BoujeeEnjinia1701/cellcheck/cad/drawings/CCK-DWG-001.pdf

CONCEPT, NOT FOR FABRICATION | CellCheck · github.com/BoujeeEnjinia1701/cellcheck

FRONT VIEW
Scale 1:5; looking at the front (along +Y)

TOP VIEW
Scale 1:5; looking down (along -Z)

RIGHT VIEW
Scale 1:5; looking at the right side (along -X)

460

300 85

ISOMETRIC VIEW
Not to scale; the cells sit under the perforated guard; seen from the front right and above, about 30 deg elevation

KEY DIMENSIONS AND INTERFACES (MM)
Unit envelope 460 x 300 x 85 on six 8 mm rubber feet
Tray 1.5 steel, liner 3; plate 1.5 Al on six 12 mm standoffs
8 channels at 40 pitch, channel 1 at x -170; cells along Y Holders take 18650 and 21700 (to 70 long, 21 dia), four-wire Guard 320 x 100 x 48.5; two M4 thumb screws
Heatsink 320 x 36 x 50: 40 fins at 8 pitch
2 fans 60 mm, finger guards, on a folded shroud on the spine ends Fan intake slots 56 x 22 in tray back wall
16 wire slots in the plate, silicone sealed
12 V DC inlet only, 6.3 A fuse; 3 A fuse per cell
Watchdog and 2.5 V comparator board (item 18) Rest rack (48 cells) and adapter stand beside the tray Mass about 4.94 kg without adapter (CCK-CAL-001) PRELIMINARY, NOT FOR FABRICATION
REV | DESCRIPTION | DATE | BY
P1 | Preliminary GA (CCK-CAL-001, CCK-DDR-001) | 2026-09-25 | AC
P2 | Constructable design: feet, standoffs, fixings (CCK-DDR-003) | 2026-10-01 | AC
P3 | Fan finger guards, silicone-sealed wire slots (CCK-DEC-001) | 2026-10-02 | AC
CELLCHECK | github.com/BoujeeEnjinia1701/cellcheck

## General arrangement, eight-channel grader

DRAWING NO.
CCK-DWG-001

REV
P3

SHEET
1 of 1

SIZE

## ANSI B

SCALE
1:5

UNITS
mm
PROJECTION | DATE
2026-10-02

DRAWN
Amish Chadha

MATERIAL / NOTES
Tray 1.5 mm steel; plate 1.5 mm Al; heatsink Al; guard 0.8 mm perforated steel. See bom/bom.csv
Licensed CERN-OHL-S-2.0 · Design Molecule Lab · designmolecule.com | Generated from cad/src; do not edit by hand
