BoujeeEnjinia1701/cellcheck/cad/drawings/CCK-DWG-101.pdf

### BUILD PLAN SKETCH, PLAN NOT YET BUILT CellCheck · github.com/BoujeeEnjinia1701/cellcheck

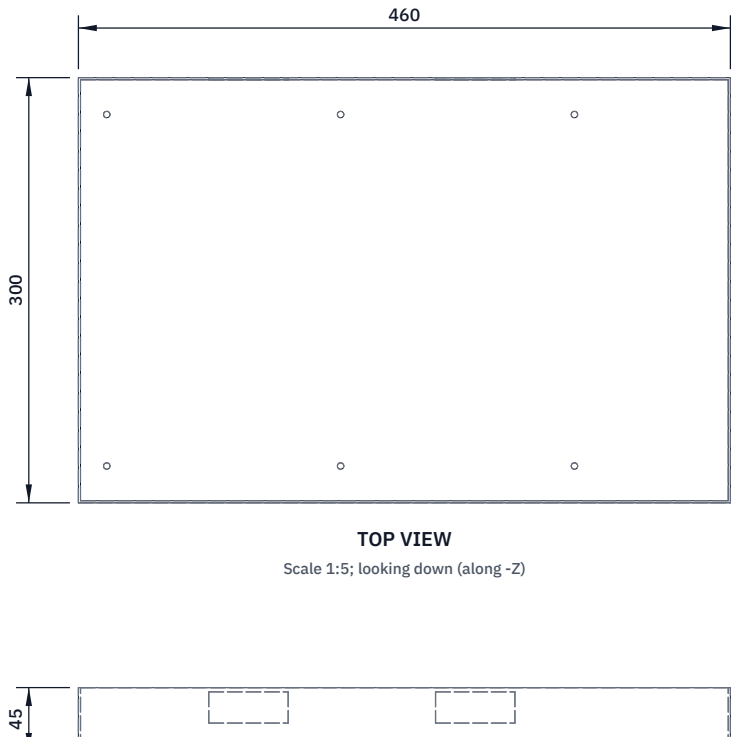
[picture p40: figure]
TOP VIEW; Scale 1:5; looking down (along -Z)

FRONT VIEW
Scale 1:5; looking at the front (along +Y)

RIGHT VIEW
Scale 1:5; looking at the right side (along -X)

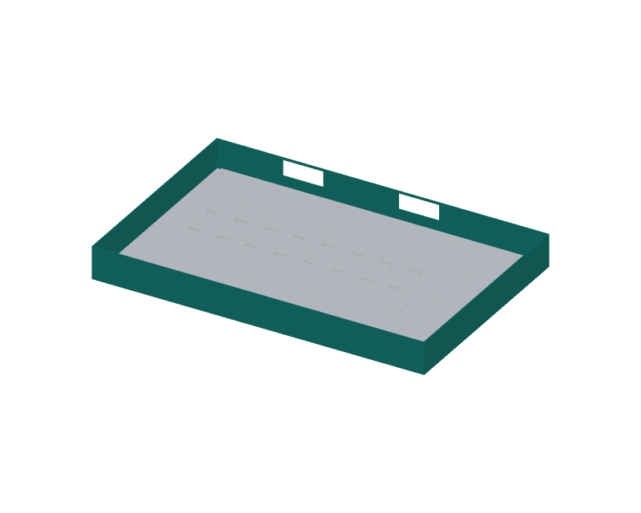
[picture p41: figure]

WHERE IT GOES
This part in colour, its neighbours in grey

HOW TO MAKE IT AND HOW IT FITS
Buy a plain steel tray about 460 x 300 x 45 mm, 1.5 mm wall, with a flat floor at least 457 x 297 mm inside. No plastic coating.
Two fan intake slots in the back wall, 56 wide x 22 tall, from 20 to 42 mm up from the floor, centred 110 mm left and 50 mm right of the centre. Drill 6 mm in each corner, cut between with a hacksaw or nibbler, file. Six 4.5 mm holes in the floor for the foot studs, 124 mm each side of
the centre line front to back, at 210 mm left, 45 mm left and
120 mm right of centre. Measure from the centre lines you scribe. Deburr every cut edge inside and out; touch up bare steel with paint. Fit: a rubber foot under each hole; its stud goes up into a standoff. Check: the six holes match the base plate's corner holes when the plate is laid on top, centred, before the liner goes in.
REV | DESCRIPTION | DATE | BY
P1 | Making sketch for the prototype build plan | 2026-10-02 | AC
CELLCHECK | github.com/BoujeeEnjinia1701/cellcheck

## CellCheck steel tray (bought, cut and drilled): making sketch

DRAWING NO.
CCK-DWG-101

REV
P1

SHEET
1 of 1

SIZE

## ANSI B

SCALE
1:5

UNITS
mm
PROJECTION | DATE
2026-10-02

DRAWN
Amish Chadha

MATERIAL / NOTES
Bought steel tray 460 x 300 x 45 mm, 1.5 mm wall
Licensed CERN-OHL-S-2.0 · Design Molecule Lab · designmolecule.com | Generated from cad/src; do not edit by hand
