BoujeeEnjinia1701/cellcheck/cad/drawings/CCK-DWG-102.pdf

### BUILD PLAN SKETCH, PLAN NOT YET BUILT CellCheck · github.com/BoujeeEnjinia1701/cellcheck

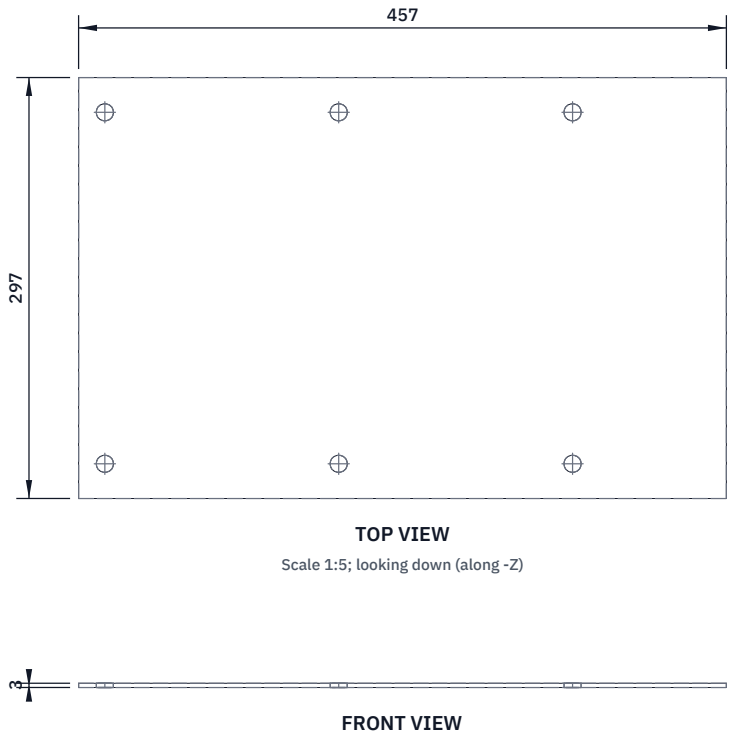
[picture p42: figure]
FRONT VIEW; TOP VIEW; Scale 1:5; looking down (along -Z)

Scale 1:5; looking at the front (along +Y)

RIGHT VIEW
Scale 1:5; looking at the right side (along -X)

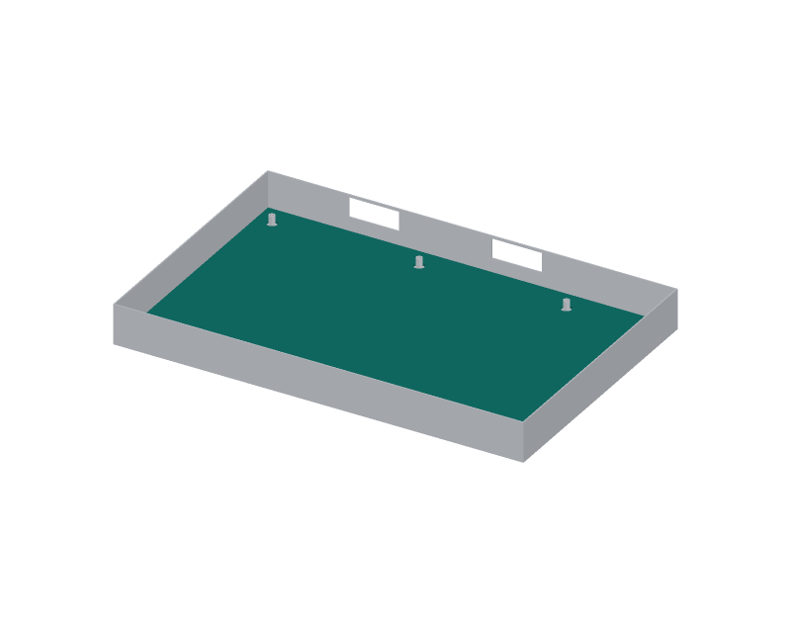
[picture p43: figure]

WHERE IT GOES
This part in colour, its neighbours in grey

HOW TO MAKE IT AND HOW IT FITS
Cut 457 x 297 mm from 3 mm ceramic fibre sheet with a sharp knife and a steel rule; trim so it lies flat on the tray floor.
Six 12 mm holes at the standoff positions (the same places as the tray's stud holes): 124 mm each side front to back, at 210 left,
45 left and 120 right of centre. Cut with a 12 mm hole punch or knife. Wear a dust mask (FFP2 or N95), gloves and long sleeves; cut outdoors or with dust extraction; wet-wipe the bench afterwards.
Fit: lies loose on the floor round the standoffs, 2 mm clear of each. Check: no tears; the floor is covered except at the six holes.
REV | DESCRIPTION | DATE | BY
P1 | Making sketch for the prototype build plan | 2026-10-02 | AC
CELLCHECK | github.com/BoujeeEnjinia1701/cellcheck

## CellCheck ceramic fibre liner: making sketch

DRAWING NO.
CCK-DWG-102

REV
P1

SHEET
1 of 1

SIZE

## ANSI B

SCALE
1:5

UNITS
mm
PROJECTION | DATE
2026-10-02

DRAWN
Amish Chadha

MATERIAL / NOTES
Ceramic fibre sheet 3 mm
Licensed CERN-OHL-S-2.0 · Design Molecule Lab · designmolecule.com | Generated from cad/src; do not edit by hand
