BoujeeEnjinia1701/cellcheck/cad/drawings/CCK-DWG-103.pdf

### BUILD PLAN SKETCH, PLAN NOT YET BUILT CellCheck · github.com/BoujeeEnjinia1701/cellcheck

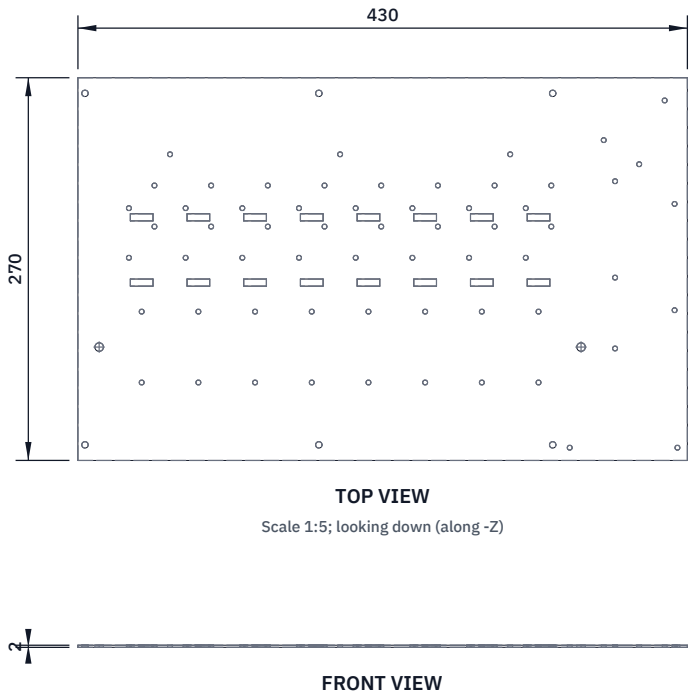
[picture p44: figure]
FRONT VIEW; TOP VIEW; Scale 1:5; looking down (along -Z)

Scale 1:5; looking at the front (along +Y)

RIGHT VIEW
Scale 1:5; looking at the right side (along -X)

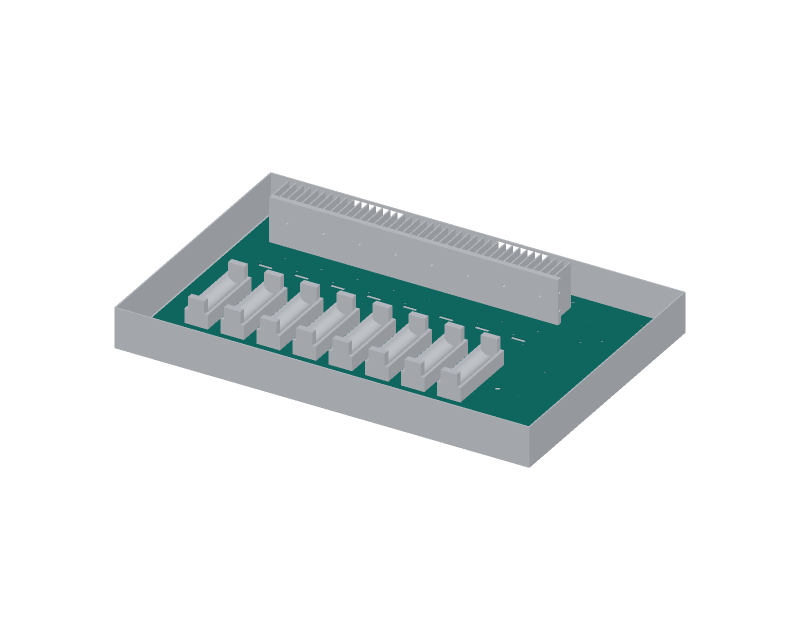
[picture p45: figure]

WHERE IT GOES
This part in colour, its neighbours in grey

HOW TO MAKE IT AND HOW IT FITS
Blank 430 x 270 mm, 1.5 mm aluminium; round the corners to 3 mm. Measure every hole from the left edge and the front edge; the
hole layout picture in the build plan gives every position.
Six 4.5 mm holes for the standoffs, 11 mm from the front and back. Per channel (eight channels, 40 mm apart, first at 45 mm from the left): two 3.4 mm holder screw holes; a 16 x 5 mm wire slot behind the holder and another between the charger and the channel board;
four 3.4 mm holes for the board standoffs.
Two 6 mm holes for the guard rivet nuts; set M4 rivet nuts in them. Three 3.4 mm heatsink screw holes; 3.4 mm holes for the right-hand bay. Slots: drill 5 mm at each end, cut between, file; fit edge grommet strip. After wiring, each slot is filled with silicone round the leads.
Check: lay the holders and heatsink on it and look through each hole.
REV | DESCRIPTION | DATE | BY
P1 | Making sketch for the prototype build plan | 2026-10-02 | AC
CELLCHECK | github.com/BoujeeEnjinia1701/cellcheck

## CellCheck base plate: making sketch

DRAWING NO.
CCK-DWG-103

REV
P1

SHEET
1 of 1

SIZE

## ANSI B

SCALE
1:5

UNITS
mm
PROJECTION | DATE
2026-10-02

DRAWN
Amish Chadha

MATERIAL / NOTES
Aluminium sheet 1.5 mm, 5052 or 6061 class
Licensed CERN-OHL-S-2.0 · Design Molecule Lab · designmolecule.com | Generated from cad/src; do not edit by hand
