BoujeeEnjinia1701/cellcheck/cad/drawings/CCK-DWG-104.pdf

### BUILD PLAN SKETCH, PLAN NOT YET BUILT CellCheck · github.com/BoujeeEnjinia1701/cellcheck

FRONT VIEW
Scale 1:2; looking at the front (along +Y)

TOP VIEW
Scale 1:2; looking down (along -Z)

RIGHT VIEW
Scale 1:2; looking at the right side (along -X)

320

36 50

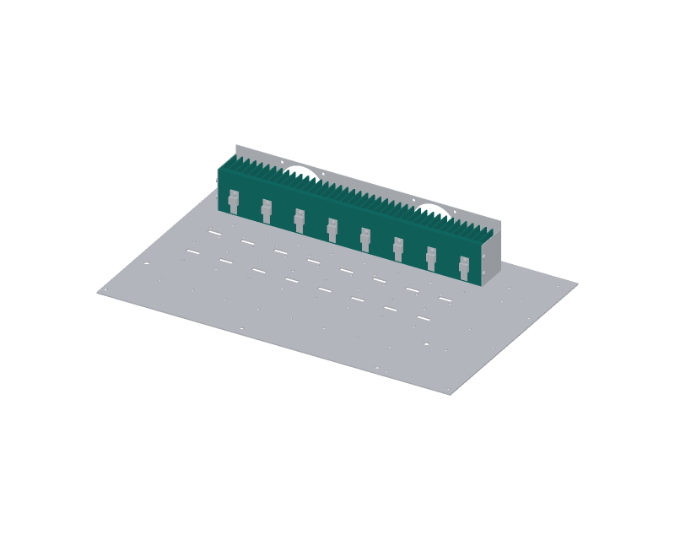
[picture p46: figure]

WHERE IT GOES
This part in colour, its neighbours in grey

HOW TO MAKE IT AND HOW IT FITS
Bought: a 6 mm spine 320 x 50 mm with 40 fins 30 mm deep at 8 mm pitch. MOSFET holes: eight M3 tapped holes through the spine (drill 2.5),
26.5 mm up from the bottom edge, 20 mm from the left end and then
every 40 mm, each midway between two fins. Deburr the front face flat. Plate screws: three M3 tapped holes 10 mm deep in the bottom edge, centred in the spine's 6 mm thickness, 40, 160 and 280 mm from the left end. Shroud screws: two M3 tapped holes 8 mm deep in each end of the spine, centred in its thickness, 15 and 35 mm up from the bottom edge.
Use cutting fluid; back the tap out often; the walls are thin.
Fit: stands on the plate, fins to the back; MOSFETs on the smooth face. Check: an M3 screw runs freely into every hole.
REV | DESCRIPTION | DATE | BY
P1 | Making sketch for the prototype build plan | 2026-10-02 | AC
CELLCHECK | github.com/BoujeeEnjinia1701/cellcheck

## CellCheck heatsink (bought, drilled and tapped): making sketch

DRAWING NO.
CCK-DWG-104

REV
P1

SHEET
1 of 1

SIZE

## ANSI B

SCALE
1:2

UNITS
mm
PROJECTION | DATE
2026-10-02

DRAWN
Amish Chadha

MATERIAL / NOTES
Aluminium finned heatsink 320 x 36 x 50 mm
Licensed CERN-OHL-S-2.0 · Design Molecule Lab · designmolecule.com | Generated from cad/src; do not edit by hand
