BoujeeEnjinia1701/cellcheck/cad/drawings/CCK-DWG-105.pdf

### BUILD PLAN SKETCH, PLAN NOT YET BUILT CellCheck · github.com/BoujeeEnjinia1701/cellcheck

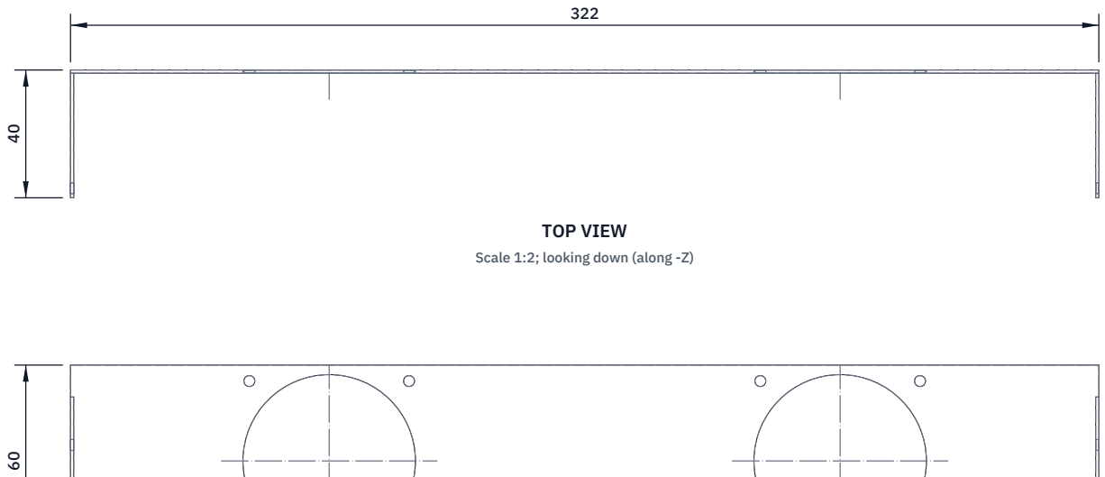
[picture p47: figure]
TOP VIEW; Scale 1:2; looking down (along -Z)
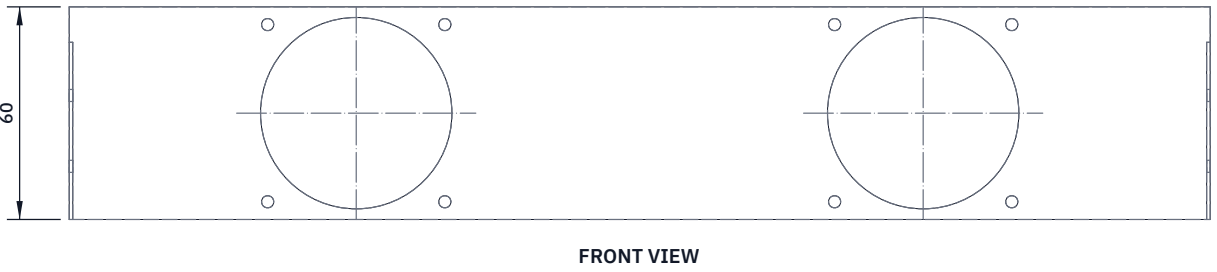
[picture p48: figure]
FRONT VIEW

Scale 1:2; looking at the front (along +Y)

RIGHT VIEW
Scale 1:2; looking at the right side (along -X)

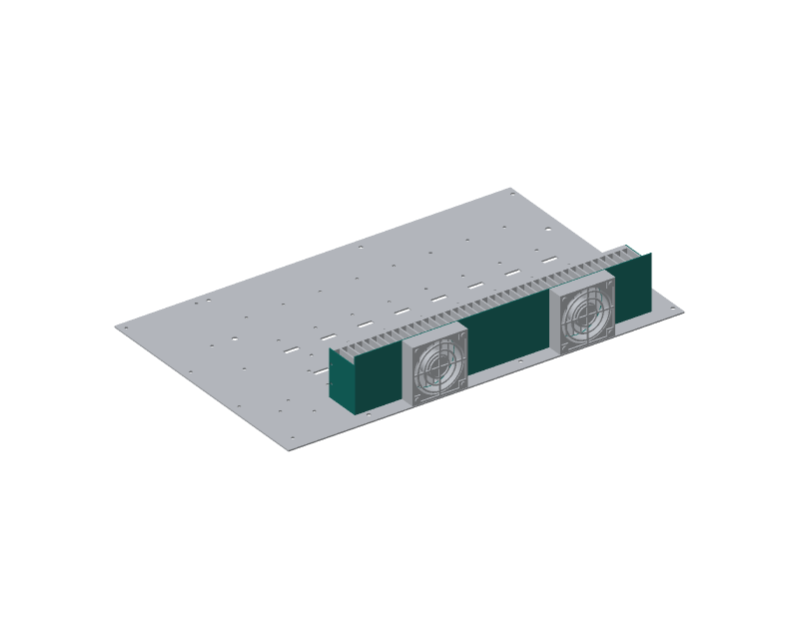
[picture p49: figure]

WHERE IT GOES
This part in colour, its neighbours in grey

HOW TO MAKE IT AND HOW IT FITS
One blank 322 x 60 mm back with a 39 x 50 mm flange on each end. Two 54 mm fan holes, centred 30 mm up, 81 mm and 241 mm from the left end of the back; cut with a hole saw or step drill.
Fan screw holes 3.4 mm on a 50 mm square round each fan hole. Fold each end flange 90 degrees forward, square to the back.
Two 3.4 mm holes in each flange, 3 mm from the free end (in line with the spine), 15 and 35 mm up from the bottom edge.
Fit the fans to the back first, screws from the inside; each fan gets a 60 mm finger guard on its outer face (four small screws). Fit: the flanges lie on the spine ends; the back stands 3 mm behind the fins; the bottom edge rests on the plate.
Check: the flange holes line up with the tapped holes in the spine.
REV | DESCRIPTION | DATE | BY
P1 | Making sketch for the prototype build plan | 2026-10-02 | AC
CELLCHECK | github.com/BoujeeEnjinia1701/cellcheck

## CellCheck fan shroud: making sketch

DRAWING NO.
CCK-DWG-105

REV
P1

SHEET
1 of 1

SIZE

## ANSI B

SCALE
1:2

UNITS
mm
PROJECTION | DATE
2026-10-02

DRAWN
Amish Chadha

MATERIAL / NOTES
Aluminium sheet 1 mm
Licensed CERN-OHL-S-2.0 · Design Molecule Lab · designmolecule.com | Generated from cad/src; do not edit by hand
