BoujeeEnjinia1701/cellcheck/cad/drawings/CCK-DWG-106.pdf

### BUILD PLAN SKETCH, PLAN NOT YET BUILT CellCheck · github.com/BoujeeEnjinia1701/cellcheck

FRONT VIEW
Scale 1:1; looking at the front (along +Y)

TOP VIEW
Scale 1:1; looking down (along -Z)

RIGHT VIEW
Scale 1:1; looking at the right side (along -X)

88

25 62

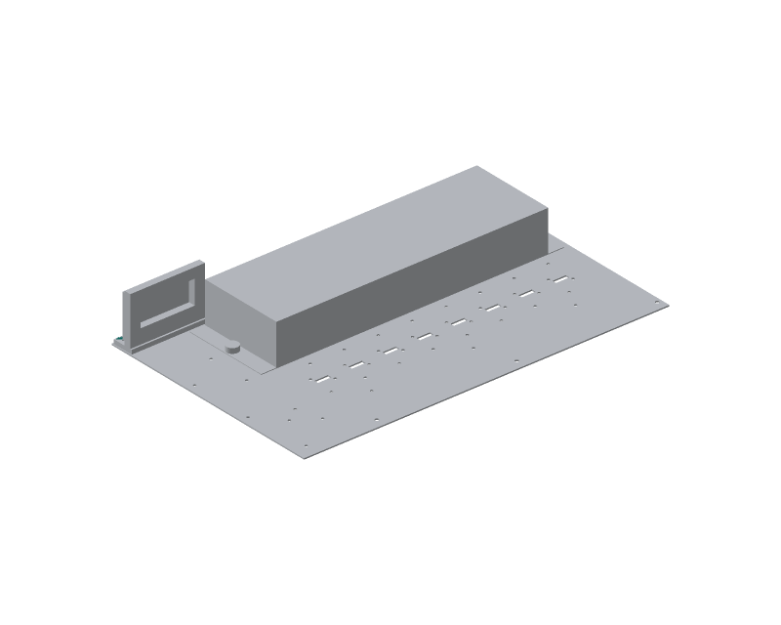
[picture p50: figure]

WHERE IT GOES
This part in colour, its neighbours in grey

HOW TO MAKE IT AND HOW IT FITS
Print: a foot 88 x 25 x 5 mm and an upright 88 x 8 x 62 mm,
15 mm back from the foot's front edge, printed lying on its back. Window 64 x 28 mm in the upright, 22 mm up, for the display's pins. Two 3 mm pilot holes in the foot, 6 mm in from each end and 7 mm from the front, for M3 screws from under the plate.
Three 7 mm holes in the foot's front strip, 25 mm apart, for the panel-mount push buttons, held by their nuts.
Fit: the display module screws to the upright's front face with its four corner holes (M2.5 or M3 self-tappers).
Check: the 86 x 50 mm display board sits flat on the upright.
REV | DESCRIPTION | DATE | BY
P1 | Making sketch for the prototype build plan | 2026-10-02 | AC
CELLCHECK | github.com/BoujeeEnjinia1701/cellcheck

## CellCheck display stand: making sketch

DRAWING NO.
CCK-DWG-106

REV
P1

SHEET
1 of 1

SIZE

## ANSI B

SCALE
1:1

UNITS
mm
PROJECTION | DATE
2026-10-02

DRAWN
Amish Chadha

MATERIAL / NOTES
PETG, 3D printed, 40 % infill
Licensed CERN-OHL-S-2.0 · Design Molecule Lab · designmolecule.com | Generated from cad/src; do not edit by hand
