BoujeeEnjinia1701/cellcheck/cad/drawings/CCK-DWG-107.pdf

### BUILD PLAN SKETCH, PLAN NOT YET BUILT CellCheck · github.com/BoujeeEnjinia1701/cellcheck

FRONT VIEW
Scale 1:1; looking at the front (along +Y)

TOP VIEW
Scale 1:1; looking down (along -Z)

RIGHT VIEW
Scale 1:1; looking at the right side (along -X)

55

40 28

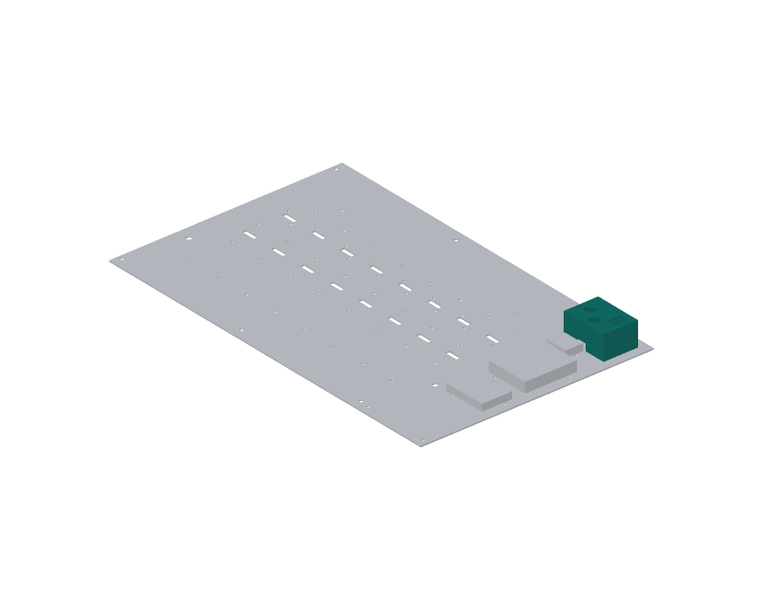
[picture p51: figure]

WHERE IT GOES
This part in colour, its neighbours in grey

HOW TO MAKE IT AND HOW IT FITS
Print an open-bottomed box 55 x 40 x 28 mm, 2 mm walls, top up. Top face: DC jack hole 11.2 mm; fuse holder hole 12 mm;
rocker switch cut-out 12 x 16 mm (check each against its datasheet). Wire exit notch 20 x 8 mm at the bottom of the front wall.
Two screw bosses inside, 6 mm in from opposite corners, 3 mm pilot holes for M3 screws from under the plate.
Fit: jack, fuse holder and switch go in from the top, nuts inside.
The adapter lead comes over the tray's right rim into the jack. Check: each part snaps or screws in square; nothing rocks.
REV | DESCRIPTION | DATE | BY
P1 | Making sketch for the prototype build plan | 2026-10-02 | AC
CELLCHECK | github.com/BoujeeEnjinia1701/cellcheck

## CellCheck inlet housing: making sketch

DRAWING NO.
CCK-DWG-107

REV
P1

SHEET
1 of 1

SIZE

## ANSI B

SCALE
1:1

UNITS
mm
PROJECTION | DATE
2026-10-02

DRAWN
Amish Chadha

MATERIAL / NOTES
PETG, 3D printed, 2 mm walls
Licensed CERN-OHL-S-2.0 · Design Molecule Lab · designmolecule.com | Generated from cad/src; do not edit by hand
