BoujeeEnjinia1701/cellcheck/cad/drawings/CCK-DWG-108.pdf

### BUILD PLAN SKETCH, PLAN NOT YET BUILT CellCheck · github.com/BoujeeEnjinia1701/cellcheck

FRONT VIEW
Scale 1:5; looking at the front (along +Y)

TOP VIEW
Scale 1:5; looking down (along -Z)

RIGHT VIEW
Scale 1:5; looking at the right side (along -X)

356

100 48

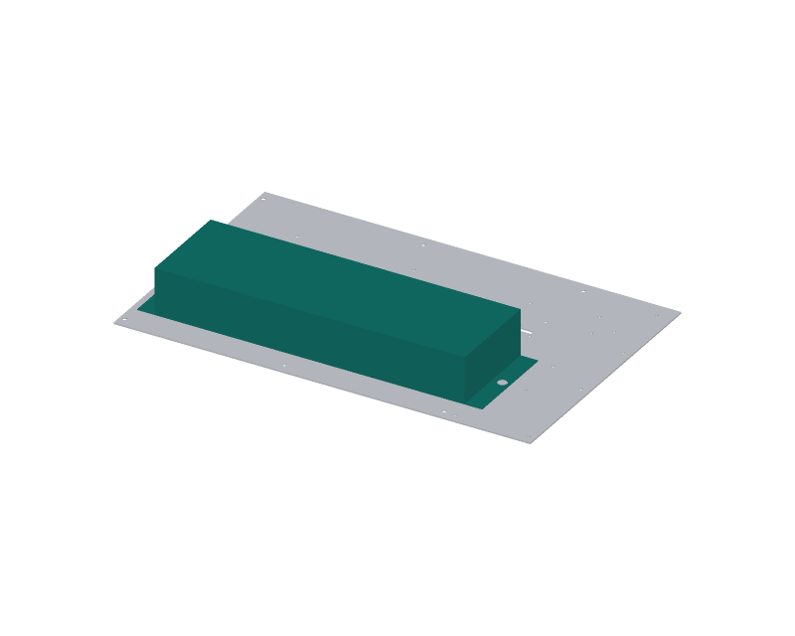
[picture p52: figure]

WHERE IT GOES
This part in colour, its neighbours in grey

HOW TO MAKE IT AND HOW IT FITS
One blank: top 320 x 100 mm in the middle; front and back
320 x 48.5 mm; ends 100 x 48.5 mm, each with an
18 mm flange; 12 mm tabs on the ends of the front and back.
Cut with aviation snips; drill 3 mm relief holes where folds cross. Fold the front, back and ends down 90 degrees; fold the tabs round the corners and rivet each with two 3.2 mm steel rivets.
Fold each end flange 90 degrees outward, flat with the bottom edge. One 10 mm hole in each flange, 10 mm out from the end wall, central. File every cut edge smooth; wear cut-resistant gloves.
Fit: open bottom on the plate over the holders; two M4 knurled thumb screws through the flanges into rivet nuts in the plate.
Check: it sits flat with no gap under any wall.
REV | DESCRIPTION | DATE | BY
P1 | Making sketch for the prototype build plan | 2026-10-02 | AC
CELLCHECK | github.com/BoujeeEnjinia1701/cellcheck

## CellCheck perforated guard: making sketch

DRAWING NO.
CCK-DWG-108

REV
P1

SHEET
1 of 1

SIZE

## ANSI B

SCALE
1:5

UNITS
mm
PROJECTION | DATE
2026-10-02

DRAWN
Amish Chadha

MATERIAL / NOTES
Perforated steel sheet 0.8 mm, about 50 % open
Licensed CERN-OHL-S-2.0 · Design Molecule Lab · designmolecule.com | Generated from cad/src; do not edit by hand
