BoujeeEnjinia1701/cellcheck/cad/drawings/CCK-DWG-109.pdf

### BUILD PLAN SKETCH, PLAN NOT YET BUILT CellCheck · github.com/BoujeeEnjinia1701/cellcheck

FRONT VIEW
Scale 2:1; looking at the front (along +Y)

TOP VIEW
Scale 2:1; looking down (along -Z)

RIGHT VIEW
Scale 2:1; looking at the right side (along -X)

24

10 17

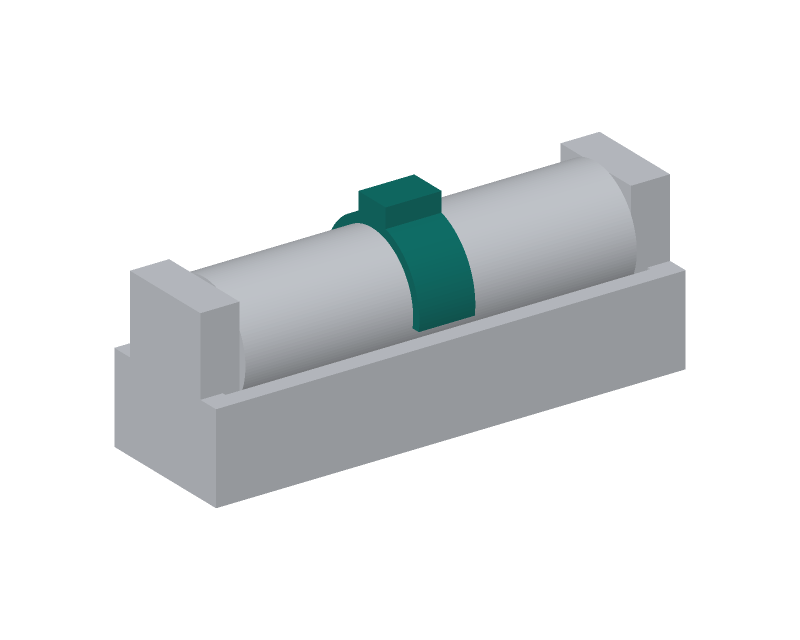
[picture p53: figure]

WHERE IT GOES
This part in colour, its neighbours in grey

HOW TO MAKE IT AND HOW IT FITS
A C-shaped ring 10 mm long, 1.6 mm wall, that springs over the top of the cell and wraps 10 degrees past its sides on each side.
21700 clip: 21.0 mm inside. 18650 clip: 18.3 mm inside.
Raised pad on top, 7 x 10 mm and 3 mm high, with a 2 mm hole down through it for the thermistor bead, which touches the cell;
a dab of thermal paste between bead and cell.
Print with the ring's axis vertical; no supports.
Fit: push down over the cell between the holder's contact posts; the lower edges stay at least 2 mm above the holder.
Check: it grips the cell and does not slide when the lead is tugged.
REV | DESCRIPTION | DATE | BY
P1 | Making sketch for the prototype build plan | 2026-10-02 | AC
CELLCHECK | github.com/BoujeeEnjinia1701/cellcheck

## CellCheck thermistor clip (print 8 for 21700, 8 for 18650): making sketch

DRAWING NO.
CCK-DWG-109

REV
P1

SHEET
1 of 1

SIZE

## ANSI B

SCALE
2:1

UNITS
mm
PROJECTION | DATE
2026-10-02

DRAWN
Amish Chadha

MATERIAL / NOTES
PETG, 3D printed, 100 % infill
Licensed CERN-OHL-S-2.0 · Design Molecule Lab · designmolecule.com | Generated from cad/src; do not edit by hand
