BoujeeEnjinia1701/cellcheck/media/card.png

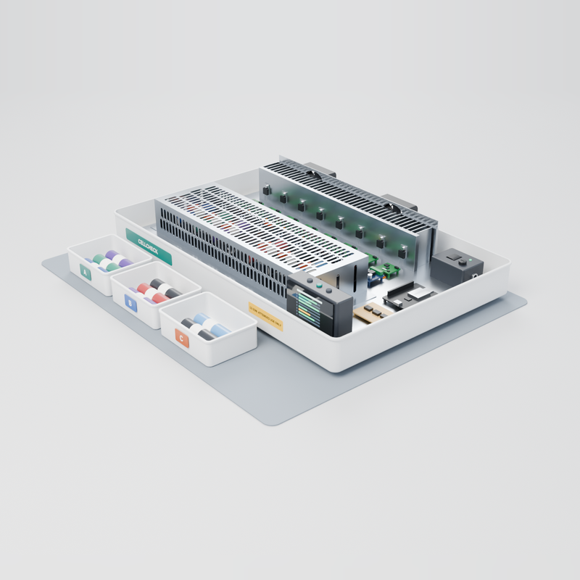
media/card.png
