BoujeeEnjinia1701/cellcheck/media/render-detail.png

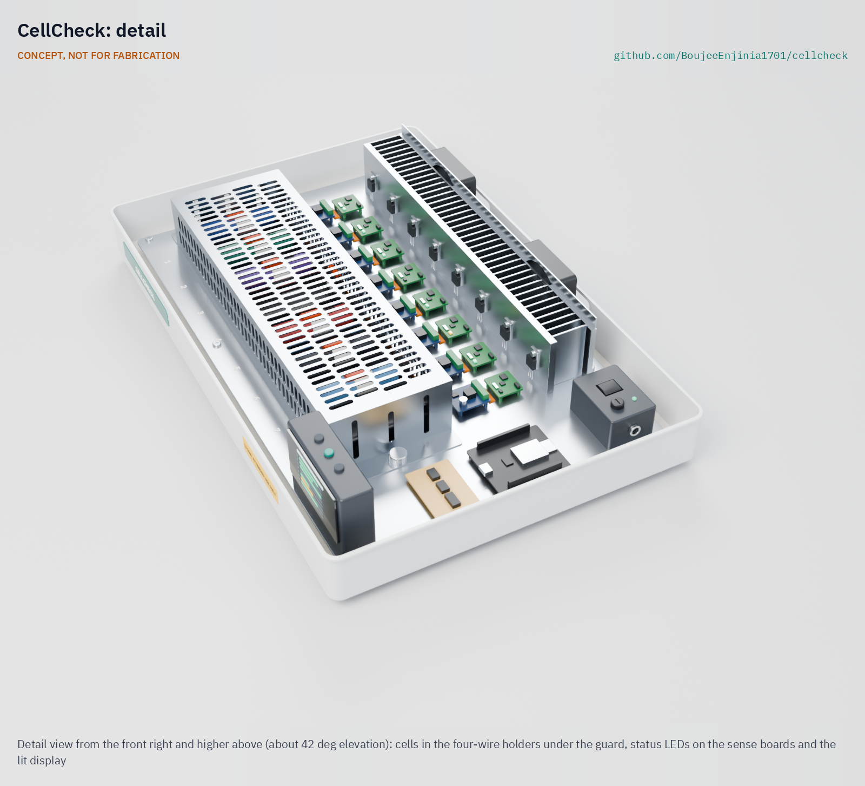
media/render-detail.png
