BoujeeEnjinia1701/cellcheck/media/render-exploded.png

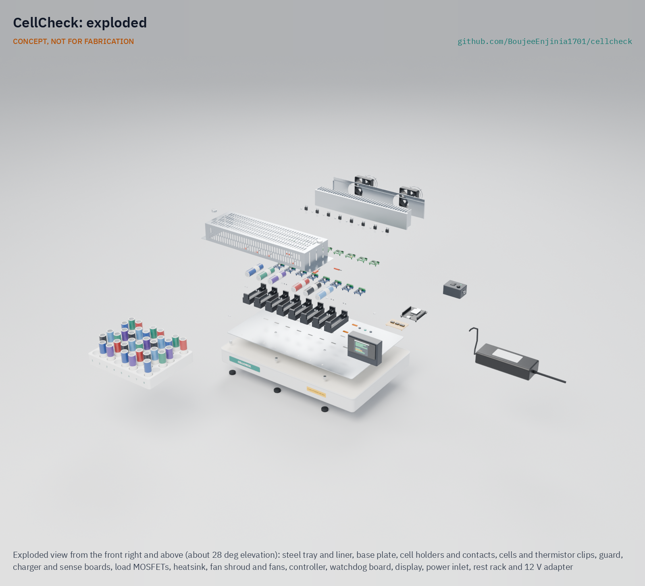
media/render-exploded.png
