BoujeeEnjinia1701/cellcheck/media/social-preview.png

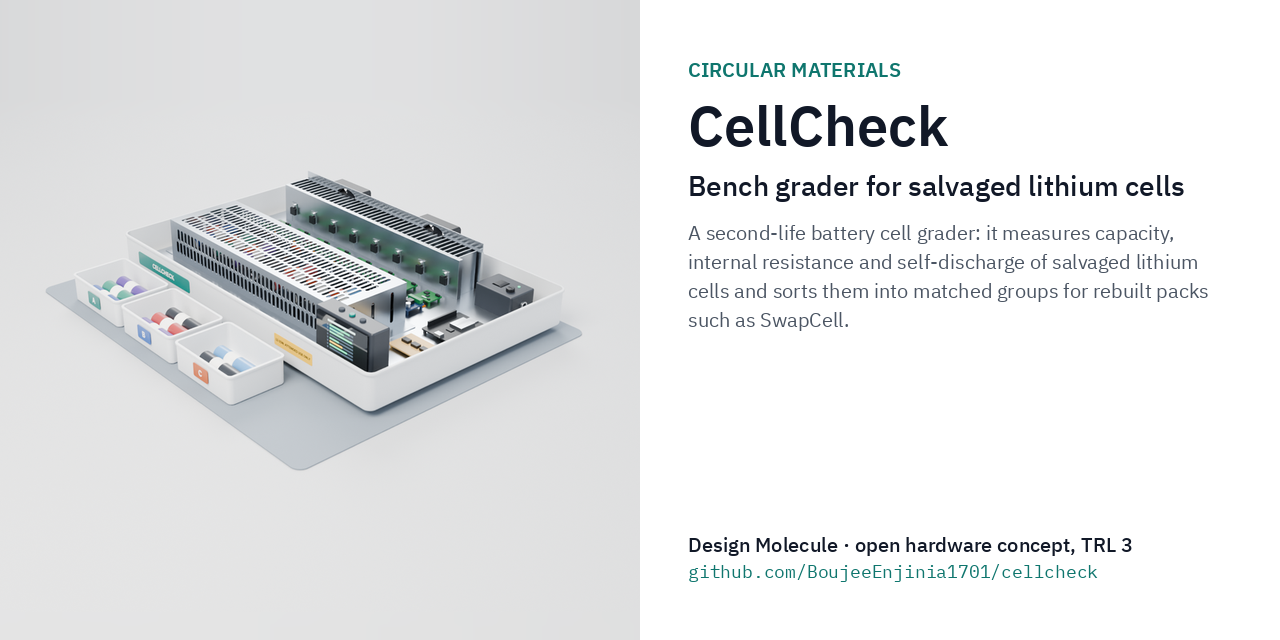
media/social-preview.png
