BoujeeEnjinia1701/cellcheck/cad/drawings/CCK-DWG-110.pdf

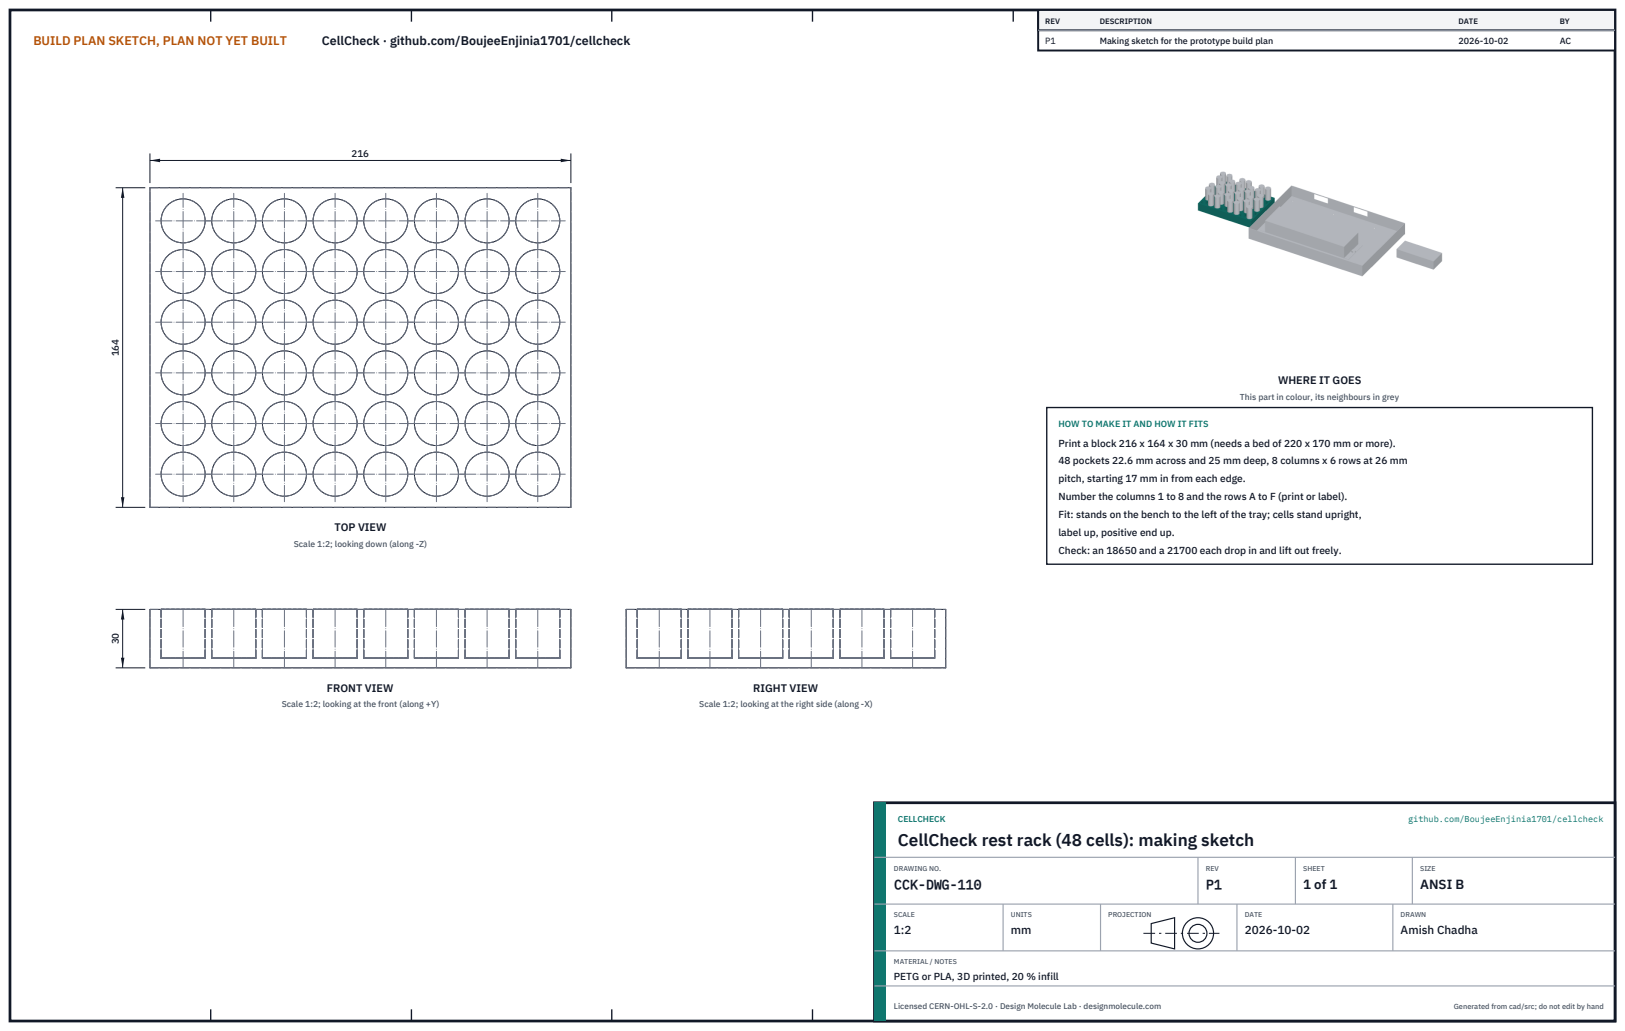
[picture p94: page 1]
BUILD PLAN SKETCH, PLAN NOT YET BUILT; CellCheck · github.com/BoujeeEnjinia1701/cellcheck; FRONT VIEW; TOP VIEW; RIGHT VIEW; REV; DESCRIPTION; DATE; Making sketch for the prototype build plan; CELLCHECK; github.com/BoujeeEnjinia1701/cellcheck; DRAWING NO. CCK-DWG-110; REV P1; SHEET 1 of 1; SIZE ANSI B; SCALE 1:2; UNITS mm; PROJECTION; DRAWN Amish Chadha; Licensed CERN-OHL-S-2.0 · Design Molecule Lab · designmolecule.com; Generated from cad/src; do not edit by hand

WHERE IT GOES

This part in colour, its neighbours in grey

HOW TO MAKE IT AND HOW IT FITS
Print a block 216 x 164 x 30 mm (needs a bed of 220 x 170 mm or more).
48 pockets 22.6 mm across and 25 mm deep, 8 columns x 6 rows at 26 mm
pitch, starting 17 mm in from each edge.
Number the columns 1 to 8 and the rows A to F (print or label).
Fit: stands on the bench to the left of the tray; cells stand upright,
label up, positive end up.
Check: an 18650 and a 21700 each drop in and lift out freely.

Scale 1:2; looking down (along -Z)

Scale 1:2; looking at the front (along +Y)

Scale 1:2; looking at the right side (along -X)

CellCheck rest rack (48 cells): making sketch

MATERIAL / NOTES
PETG or PLA, 3D printed, 20 % infill
